thenfour/Clarinoid/CAD/korg microkey-37/switch info.xlsx

switch | contact diode | wire | multiplex channel | selA,B,C | iC Sel | enable | READ
SW1 | D1 | 3 | y3_a | y3 | a | 1 | wire3
SW1 | D2 | 4 | y3_a
SW2 | D3 | 5 | y3_a
SW2 | D4 | 6 | y3_a
SW3 | D5 | 7 | y3_a
SW3 | D6 | 8 | y3_a
SW4 | D7 | 9 | y3_a
SW4 | D8 | 10 | y3_a
SW5 | D9 | 3 | y4_a
SW5 | D10 | 4 | y4_a
SW6 | D11 | 5 | y4_a
SW6 | D12 | 6 | y4_a
SW7 | D13 | 7 | y4_a
SW7 | D14 | 8 | y4_a
SW8 | D15 | 9 | y4_a
SW8 | D16 | 10 | y4_a
SW9 | D17 | 3 | y5_a
SW9 | D18 | 4 | y5_a
SW10 | D19 | 5 | y5_a
SW10 | D20 | 6 | y5_a
SW11 | D21 | 7 | y5_a
SW11 | D22 | 8 | y5_a
SW12 | D23 | 9 | y5_a
SW12 | D24 | 10 | y5_a
SW13 | D25 | 3 | y6_a
SW13 | D26 | 4 | y6_a
SW14 | D27 | 5 | y6_a
SW14 | D28 | 6 | y6_a
SW15 | D29 | 7 | y6_a
SW15 | D30 | 8 | y6_a
SW16 | D31 | 9 | y6_a
SW16 | D32 | 10 | y6_a
SW17 | D33 | 3 | y7_a
SW17 | D34 | 4 | y7_a
SW18 | D35 | 5 | y7_a
SW18 | D36 | 6 | y7_a
SW19 | D37 | 7 | y7_a
SW19 | D38 | 8 | y7_a
SW20 | D39 | 9 | y7_a
SW20 | D40 | 10 | y7_a
SW21 | D41 | 3 | y0_b
SW21 | D42 | 4 | y0_b
SW22 | D43 | 5 | y0_b
SW22 | D44 | 6 | y0_b
SW23 | D45 | 7 | y0_b
SW23 | D46 | 8 | y0_b
SW24 | D47 | 9 | y0_b
SW24 | D48 | 10 | y0_b
SW25 | D49 | 3 | y1_b
SW25 | D50 | 4 | y1_b
SW26 | D51 | 5 | y1_b
SW26 | D52 | 6 | y1_b
SW27 | D53 | 7 | y1_b
SW27 | D54 | 8 | y1_b
SW28 | D55 | 9 | y1_b
SW28 | D56 | 10 | y1_b
SW29 | D57 | 3 | y2_b
SW29 | D58 | 4 | y2_b
SW30 | D59 | 5 | y2_b
SW30 | D60 | 6 | y2_b
SW31 | D61 | 7 | y2_b
SW31 | D62 | 8 | y2_b
SW32 | D63 | 9 | y2_b
SW32 | D64 | 10 | y2_b
SW33 | D65 | 3 | y3_b
SW33 | D66 | 4 | y3_b
SW34 | D67 | 5 | y3_b
SW34 | D68 | 6 | y3_b
SW35 | D69 | 7 | y3_b
SW35 | D70 | 8 | y3_b
SW36 | D71 | 9 | y3_b
SW36 | D72 | 10 | y3_b
SW37 | D73 | 3 | y4_b
SW37 | D74 | 4 | y4_b
