thenfour/Clarinoid/src/clarinoid/basic/Serialization.hpp

// TODO: maximum string size and possibly other sanity checks

#pragma once

#include <type_traits>
#include "BaseDefs.hpp"

#ifdef CLARINOID_PLATFORM_X86
#include <map>
#endif

namespace clarinoid
{

struct IStream
{
    virtual size_t write(const uint8_t *buf, size_t bytes) = 0;
    virtual size_t read(uint8_t *buf, size_t bytes) = 0;
    virtual int readByte() = 0;
    virtual size_t flushWrite() = 0;
};

struct StreamStream : IStream
{
    ::Stream &mStream;
    StreamStream(::Stream &s) : mStream(s)
    {
    }
    virtual size_t write(const uint8_t *buf, size_t bytes) override
    {
        return mStream.write(buf, bytes);
    }

    virtual size_t read(uint8_t *buf, size_t bytes) override
    {
        return mStream.readBytes((char *)buf, bytes);
    }

    virtual int readByte() override
    {
        uint8_t ret;
        return !!read(&ret, 1) ? (int)ret : (int)-1;
    }
    virtual size_t flushWrite() override
    {
        return 0;
    }
};

struct IPeekableStream : IStream
{
    // return <0 if failure
    virtual int peekByte() = 0;
};

struct BufferedStream : IPeekableStream
{
    static constexpr size_t BufferSize = gBufferedStreamBufferSize;
    IStream &mStream;
    uint8_t mBuffer[BufferSize]{0};
    size_t mBufferUsed = 0;
    size_t mReadBufferCursor = 0;

    BufferedStream(IStream &stream) : mStream(stream)
    {
    }

    virtual size_t write(const uint8_t *buf, size_t bytes) override
    {
        size_t ret = 0;
        while (bytes > 0)
        {
            size_t toWriteToBuffer = std::min(bytes, BufferSize - mBufferUsed);
            memcpy(mBuffer + mBufferUsed, buf, toWriteToBuffer);
            mBufferUsed += toWriteToBuffer;
            ret += toWriteToBuffer;
            if (mBufferUsed >= BufferSize)
            {
                size_t written = flushWrite();
                if (written != BufferSize)
                {
                    // something went wrong with underlying stream. likely unusable past this state.
                    int bytesFailed = (int)BufferSize - (int)written;
                    return ret - bytesFailed;
                }
            }
            buf += toWriteToBuffer;
            bytes -= toWriteToBuffer;
        }
        return ret;
    }

    virtual int readByte() override
    {
        uint8_t ret;
        return !!read(&ret, 1) ? (int)ret : (int)-1;
    }

    virtual size_t flushWrite() override
    {
        size_t ret = mStream.write(mBuffer, mBufferUsed);
        mBufferUsed = 0;
        return ret;
    }

    virtual size_t read(uint8_t *buf, size_t bytes) override
    {
        size_t ret = 0;
        while (bytes && EnsureBufferHasUnreadContent())
        {
            size_t unreadBufferBytes = mBufferUsed - mReadBufferCursor;
            size_t bufferBytesToRead = std::min(bytes, unreadBufferBytes);
            memcpy(buf, mBuffer + mReadBufferCursor, bufferBytesToRead);
            mReadBufferCursor += bufferBytesToRead;
            ret += bufferBytesToRead;
            buf += bufferBytesToRead;
            bytes -= bufferBytesToRead;
        }
        return ret;
    }

    virtual int peekByte() override
    {
        if (!EnsureBufferHasUnreadContent())
        {
            return -1;
        }
        return mBuffer[mReadBufferCursor];
    }

    // tries to make sure there's at least 1 unbyte in the buffer.
    // if unable to get even 1 byte, returns false.
    bool EnsureBufferHasUnreadContent()
    {
        // if there's no more buffer to read
        if (mReadBufferCursor >= mBufferUsed)
        {
            // get a fresh buffer.
            mBufferUsed = mStream.read(mBuffer, BufferSize);
            mReadBufferCursor = 0;
            return mBufferUsed > 0;
        }
        return mBufferUsed != 0;
    }
};

enum class TokenType
{
    Syntax,
    Whitespace,
    Keyname,
    StringVal,
    EnumStringVal,
    NumberVal,
    Null,
    BoolValue,
};

struct TextStream : IPeekableStream
{
    IPeekableStream &mStream;
    // 1-based per convention
    uint32_t mLine = 1;
    uint32_t mColumn = 1;
    
    bool mMinified = true;

    TextStream(IPeekableStream &stream) : mStream(stream)
    {
    }

  private:
    virtual size_t write(const uint8_t *buf, size_t bytes) override
    {
        return mStream.write(buf, bytes);
    }

    virtual size_t read(uint8_t *buf, size_t bytes) override
    {
        return mStream.read(buf, bytes);
    }

  public:
#ifdef CLARINOID_PLATFORM_X86

    static const char *TokenTypeToString(TokenType t)
    {
        switch (t)
        {
        case TokenType::Keyname:
            return "keyname";
        case TokenType::EnumStringVal:
            return "enum   ";
        case TokenType::NumberVal:
            return "number ";
        case TokenType::StringVal:
            return "string ";
        case TokenType::Syntax:
            return "syntax ";
        case TokenType::Whitespace:
            return "whites ";
        case TokenType::Null:
            return "null   ";
        case TokenType::BoolValue:
            return "boolval";
        }
        return "?";
    }

    struct SpecificTokenInfo
    {
        std::string mToken;
        int mBytes;
    };

    struct TokenInfo
    {
        std::map<std::string, SpecificTokenInfo> mWrites;
        int mBytes = 0;
    };

    std::map<TokenType, TokenInfo> mStats;

    void DumpStats()
    {
        std::cout << std::endl;
        int total = 0;
        for (auto &kv : mStats)
        {
            std::cout << TokenTypeToString(kv.first) << ": " << kv.second.mBytes << " bytes" << std::endl;

            std::vector<TextStream::SpecificTokenInfo> writes;
            for (auto &tokinfo : kv.second.mWrites)
            {
                writes.push_back(tokinfo.second);
            }

            auto sortFn = [](const TextStream::SpecificTokenInfo &a, const TextStream::SpecificTokenInfo &b) -> bool {
                return a.mBytes > b.mBytes;
            };

            std::sort(writes.begin(), writes.end(), sortFn);

            for (size_t i = 0; i < std::min((size_t)20, writes.size()); ++i)
            {
                std::cout << "    "  << writes[i].mBytes << ": " << writes[i].mToken << std::endl;
            }

            total += kv.second.mBytes;
        }
        std::cout << total << " total bytes " << std::endl;



    }

    std::string mIncompleteStringToken;
    bool mIsCollectingString = false;
    TokenType mCollectingType = TokenType::StringVal; // doesn't matter.

    void BeginToken(TokenType type)
    {
        CCASSERT(!mIsCollectingString);
        mIncompleteStringToken.clear();
        mIsCollectingString = true;
        mCollectingType = type;
    }
    void EndToken()
    {
        CCASSERT(mIsCollectingString);
        mIsCollectingString = false;
        CollectStat(mIncompleteStringToken.c_str(), mCollectingType);
        mIncompleteStringToken.clear();
    }

    void CollectStat(const String &s, TokenType type)
    {
        if (mIsCollectingString)
        {
            mIncompleteStringToken += s.c_str();
        }
        else
        {
            auto &info = mStats[type];
            info.mBytes += (int)s.length();
            auto &sinfo = info.mWrites[s.c_str()];
            sinfo.mBytes += (int)s.length();
            sinfo.mToken = s.c_str();
        }
    }

#else
    void BeginToken(TokenType type)
    {
    }
    void EndToken()
    {
    }

#endif

    size_t write(const String &s, TokenType type)
    {
        if ((type == TokenType::Whitespace) && mMinified)
            return s.length();

#ifdef CLARINOID_PLATFORM_X86
        CollectStat(s, type);
#endif

        size_t ret = mStream.write((const uint8_t *)s.c_str(), s.length());
        for (size_t i = 0; i < ret; ++i)
        {
            interpretChar(s[i]);
        }
        return ret;
    }

    // Reads one byte, or returns -1
    virtual int readByte() override
    {
        int ch = mStream.readByte();
        if (ch <= 0)
            return ch;
        interpretChar(ch);
        return ch;
    }

    virtual int peekByte() override
    {
        return mStream.peekByte();
    }

    virtual size_t flushWrite() override
    {
        return mStream.flushWrite();
    }

  private:
    void interpretChar(char ch)
    {
        if (ch == '\n')
        {
            mLine++;
            mColumn = 1;
            return;
        }
        mColumn++;
    }
};

namespace CCJSON
{

    bool gQuoteKeyNames = false;

template <typename T, typename F_>
T alias_cast(F_ raw_data)
{
    union {
        F_ raw;
        T data;
    } z;
    z.raw = raw_data;
    return z.data;
}

template <bool Condition, class TrueType, class FalseType>
struct conditional
{
    typedef TrueType type;
};

template <class TrueType, class FalseType>
struct conditional<false, TrueType, FalseType>
{
    typedef FalseType type;
};

template <typename A, typename B>
struct choose_largest : conditional<(sizeof(A) > sizeof(B)), A, B>
{
};

typedef double Float;
typedef int64_t Integer;
typedef uint64_t UInt;

enum class NumberType : uint8_t
{
    Undefined,
    Float,
    Integer,
    UInteger,
};

struct EscapeSequence
{
    // returns the json char after escape slash, for the given string character.
    // returns 0 if this char does not need escaping.
    static char escapeChar(char c)
    {
        const char *p = escapeTable(true);
        while (p[0] && p[1] != c)
        {
            p += 2;
        }
        return p[0];
    }
    // accepts a json char after slash, and returns the actual string char.
    // returns 0 if this is not a recognized escape sequence.
    static char unescapeChar(char c)
    {
        const char *p = escapeTable(false);
        for (;;)
        {
            if (p[0] == '\0')
                return 0;
            if (p[0] == c)
                return p[1];
            p += 2;
        }
    }

  private:
    static const char *escapeTable(bool excludeSolidus)
    {
        // groups of 2 chars; 1st char is the incoming char after an escape char ('\')
        // 2nd char is the actual char to output.
        return &"//\"\"\\\\b\bf\fn\nr\rt\t"[excludeSolidus ? 2 : 0];
    }
};

template <typename T, size_t = sizeof(T)>
struct FloatTraits
{
};

template <typename T>
struct FloatTraits<T, sizeof(double)>
{
    typedef uint64_t mantissa_type;
    static const short mantissa_bits = 52;
    static const mantissa_type mantissa_max = (mantissa_type(1) << mantissa_bits) - 1;

    typedef int16_t exponent_type;
    static const exponent_type exponent_max = 308;

    template <typename TExponent>
    static T make_float(T m, TExponent e)
    {
        if (e > 0)
        {
            for (uint8_t index = 0; e != 0; index++)
            {
                if (e & 1)
                    m *= positiveBinaryPowerOfTen(index);
                e >>= 1;
            }
        }
        else
        {
            e = TExponent(-e);
            for (uint8_t index = 0; e != 0; index++)
            {
                if (e & 1)
                    m *= negativeBinaryPowerOfTen(index);
                e >>= 1;
            }
        }
        return m;
    }

    static T positiveBinaryPowerOfTen(int index)
    {
        static uint32_t const factors[] PROGMEM = {
            0x40240000,
            0x00000000, // 1e1
            0x40590000,
            0x00000000, // 1e2
            0x40C38800,
            0x00000000, // 1e4
            0x4197D784,
            0x00000000, // 1e8
            0x4341C379,
            0x37E08000, // 1e16
            0x4693B8B5,
            0xB5056E17, // 1e32
            0x4D384F03,
            0xE93FF9F5, // 1e64
            0x5A827748,
            0xF9301D32, // 1e128
            0x75154FDD,
            0x7F73BF3C // 1e256
        };
        return forge(factors[2 * index], factors[2 * index + 1]);
    }

    static T negativeBinaryPowerOfTen(int index)
    {
        static uint32_t const factors[] PROGMEM = {
            0x3FB99999,
            0x9999999A, // 1e-1
            0x3F847AE1,
            0x47AE147B, // 1e-2
            0x3F1A36E2,
            0xEB1C432D, // 1e-4
            0x3E45798E,
            0xE2308C3A, // 1e-8
            0x3C9CD2B2,
            0x97D889BC, // 1e-16
            0x3949F623,
            0xD5A8A733, // 1e-32
            0x32A50FFD,
            0x44F4A73D, // 1e-64
            0x255BBA08,
            0xCF8C979D, // 1e-128
            0x0AC80628,
            0x64AC6F43 // 1e-256
        };
        return forge(factors[2 * index], factors[2 * index + 1]);
    }

    static T negativeBinaryPowerOfTenPlusOne(int index)
    {
        static uint32_t const factors[] PROGMEM = {
            0x3FF00000,
            0x00000000, // 1e0
            0x3FB99999,
            0x9999999A, // 1e-1
            0x3F50624D,
            0xD2F1A9FC, // 1e-3
            0x3E7AD7F2,
            0x9ABCAF48, // 1e-7
            0x3CD203AF,
            0x9EE75616, // 1e-15
            0x398039D6,
            0x65896880, // 1e-31
            0x32DA53FC,
            0x9631D10D, // 1e-63
            0x25915445,
            0x81B7DEC2, // 1e-127
            0x0AFE07B2,
            0x7DD78B14 // 1e-255
        };
        return forge(factors[2 * index], factors[2 * index + 1]);
    }

    static T nan()
    {
        return forge(0x7ff80000, 0x00000000);
    }

    static T inf()
    {
        return forge(0x7ff00000, 0x00000000);
    }

    static T highest()
    {
        return forge(0x7FEFFFFF, 0xFFFFFFFF);
    }

    static T lowest()
    {
        return forge(0xFFEFFFFF, 0xFFFFFFFF);
    }

    // constructs a double floating point values from its binary representation
    // we use this function to workaround platforms with single precision literals
    // (for example, when -fsingle-precision-constant is passed to GCC)
    static T forge(uint32_t msb, uint32_t lsb)
    {
        return alias_cast<T>((uint64_t(msb) << 32) | lsb);
    }
};

// specialization for 32-bit floats
template <typename T>
struct FloatTraits<T, sizeof(float)>
{
    typedef uint32_t mantissa_type;
    static const short mantissa_bits = 23;
    static const mantissa_type mantissa_max = (mantissa_type(1) << mantissa_bits) - 1;

    typedef int8_t exponent_type;
    static const exponent_type exponent_max = 38;

    template <typename TExponent>
    static T make_float(T m, TExponent e)
    {
        if (e > 0)
        {
            for (uint8_t index = 0; e != 0; index++)
            {
                if (e & 1)
                    m *= positiveBinaryPowerOfTen(index);
                e >>= 1;
            }
        }
        else
        {
            e = -e;
            for (uint8_t index = 0; e != 0; index++)
            {
                if (e & 1)
                    m *= negativeBinaryPowerOfTen(index);
                e >>= 1;
            }
        }
        return m;
    }

    static T positiveBinaryPowerOfTen(int index)
    {
        static uint32_t const factors[] PROGMEM = {
            0x41200000, // 1e1f
            0x42c80000, // 1e2f
            0x461c4000, // 1e4f
            0x4cbebc20, // 1e8f
            0x5a0e1bca, // 1e16f
            0x749dc5ae  // 1e32f
        };
        return forge(factors[index]);
    }

    static T negativeBinaryPowerOfTen(int index)
    {
        static uint32_t const factors[] PROGMEM = {
            0x3dcccccd, // 1e-1f
            0x3c23d70a, // 1e-2f
            0x38d1b717, // 1e-4f
            0x322bcc77, // 1e-8f
            0x24e69595, // 1e-16f
            0x0a4fb11f  // 1e-32f
        };
        return forge(factors[index]);
    }

    static T negativeBinaryPowerOfTenPlusOne(int index)
    {
        static uint32_t const factors[] PROGMEM = {
            0x3f800000, // 1e0f
            0x3dcccccd, // 1e-1f
            0x3a83126f, // 1e-3f
            0x33d6bf95, // 1e-7f
            0x26901d7d, // 1e-15f
            0x0c01ceb3  // 1e-31f
        };
        return forge(factors[index]);
    }

    static T forge(uint32_t bits)
    {
        return alias_cast<T>(bits);
    }

    static T nan()
    {
        return forge(0x7fc00000);
    }

    static T inf()
    {
        return forge(0x7f800000);
    }

    static T highest()
    {
        return forge(0x7f7fffff);
    }

    static T lowest()
    {
        return forge(0xFf7fffff);
    }
};

template <typename TFloat>
struct FloatParts
{
    uint32_t integral;
    uint32_t decimal;
    int16_t exponent;
    int8_t decimalPlaces;

    // Control the exponentiation threshold for big numbers
    // CAUTION: cannot be more that 1e9 !!!!
    static constexpr TFloat POSITIVE_EXPONENTIATION_THRESHOLD = TFloat(1e7);
    static constexpr TFloat NEGATIVE_EXPONENTIATION_THRESHOLD = TFloat(1e-5);

    FloatParts(TFloat value)
    {
        uint32_t maxDecimalPart = sizeof(TFloat) >= 8 ? 1000000000 : 1000000;
        decimalPlaces = sizeof(TFloat) >= 8 ? 9 : 6;

        exponent = normalize(value);

        integral = uint32_t(value);
        // reduce number of decimal places by the number of integral places
        for (uint32_t tmp = integral; tmp >= 10; tmp /= 10)
        {
            maxDecimalPart /= 10;
            decimalPlaces--;
        }

        TFloat remainder = (value - TFloat(integral)) * TFloat(maxDecimalPart);

        decimal = uint32_t(remainder);
        remainder = remainder - TFloat(decimal);

        // rounding:
        // increment by 1 if remainder >= 0.5
        decimal += uint32_t(remainder * 2);
        if (decimal >= maxDecimalPart)
        {
            decimal = 0;
            integral++;
            if (exponent && integral >= 10)
            {
                exponent++;
                integral = 1;
            }
        }

        // remove trailing zeros
        while (decimal % 10 == 0 && decimalPlaces > 0)
        {
            decimal /= 10;
            decimalPlaces--;
        }
    }

    static int16_t normalize(TFloat &value)
    {
        typedef FloatTraits<TFloat> traits;
        int16_t powersOf10 = 0;

        int8_t index = sizeof(TFloat) == 8 ? 8 : 5;
        int bit = 1 << index;

        if (value >= POSITIVE_EXPONENTIATION_THRESHOLD)
        {
            for (; index >= 0; index--)
            {
                if (value >= traits::positiveBinaryPowerOfTen(index))
                {
                    value *= traits::negativeBinaryPowerOfTen(index);
                    powersOf10 = int16_t(powersOf10 + bit);
                }
                bit >>= 1;
            }
        }

        if (value > 0 && value <= NEGATIVE_EXPONENTIATION_THRESHOLD)
        {
            for (; index >= 0; index--)
            {
                if (value < traits::negativeBinaryPowerOfTenPlusOne(index))
                {
                    value *= traits::positiveBinaryPowerOfTen(index);
                    powersOf10 = int16_t(powersOf10 - bit);
                }
                bit >>= 1;
            }
        }

        return powersOf10;
    }
};

String UnsignedIntegerToStringWithOptionalPrefix(UInt value, char prefixChar = 0)
{
    char buffer[24] = {0};
    char *end = buffer + sizeof(buffer) - 1;
    char *begin = end;

    // write the string in reverse order
    do
    {
        *--begin = char(value % 10 + '0');
        value = UInt(value / 10);
    } while (value);

    if (prefixChar)
    {
        *--begin = prefixChar;
    }

    return {begin};
}

String UnsignedIntegerToString(UInt value)
{
    return UnsignedIntegerToStringWithOptionalPrefix(value, 0);
}

String SignedIntegerToString(Integer value)
{
    String ret;
    if (value < 0)
    {
        UInt unsigned_value = UInt(UInt(~value) + 1);
        return ret + UnsignedIntegerToStringWithOptionalPrefix(unsigned_value, '-');
    }
    return UnsignedIntegerToStringWithOptionalPrefix(UInt(value), 0);
}

struct NumberData
{
    NumberType mType = NumberType::Undefined;
    Float mFloatValue = 0;
    Integer mIntValue = 0;
    UInt mUIntValue = 0;

    template <typename T, std::enable_if_t<std::is_floating_point<T>::value, int> = 0>
    void Set(T param)
    {
        mFloatValue = param;
        mType = NumberType::Float;
    }

    template <typename T, std::enable_if_t<std::is_integral<T>::value && std::is_signed<T>::value, int> = 0>
    void Set(T param)
    {
        mIntValue = param;
        mType = NumberType::Integer;
    }

    template <typename T, std::enable_if_t<std::is_integral<T>::value && std::is_unsigned<T>::value, int> = 0>
    void Set(T param)
    {
        mUIntValue = param;
        mType = NumberType::UInteger;
    }

    template <typename T, std::enable_if_t<std::is_floating_point<T>::value || std::is_integral<T>::value, int> = 0>
    T Get() const
    {
        switch (mType)
        {
        case NumberType::Undefined:
        default:
            return 0;
        case NumberType::Float:
            return T(mFloatValue);
        case NumberType::Integer:
            return T(mIntValue);
        case NumberType::UInteger:
            return T(mUIntValue);
        }
    }

    String ToString() const
    {
        switch (mType)
        {
        default:
            return "<invalid;fatal error>";
        case NumberType::Undefined:
            return "<undefined>";
        case NumberType::Float:
            return String("<float>:") + String(mFloatValue);
        case NumberType::Integer:
            return String("<signed>:") + SignedIntegerToString(mIntValue);
        case NumberType::UInteger:
            return String("<unsigned>:") + UnsignedIntegerToString(mUIntValue);
        }
    }
};

// this could be adapted to read from stream, char by char, but it's just simpler to go like this.
inline bool parseNumber(const char *s, NumberData &result)
{
    typedef FloatTraits<Float> traits;
    typedef choose_largest<traits::mantissa_type, UInt>::type mantissa_t;
    typedef traits::exponent_type exponent_t;

    CCASSERT(s != 0);

    bool is_negative = false;
    switch (*s)
    {
    case '-':
        is_negative = true;
        s++;
        break;
    case '+':
        s++;
        break;
    }

    if (!isdigit(*s) && *s != '.')
        return false;

    mantissa_t mantissa = 0;
    exponent_t exponent_offset = 0;
    const mantissa_t maxUint = UInt(-1);

    while (isdigit(*s))
    {
        uint8_t digit = uint8_t(*s - '0');
        if (mantissa > maxUint / 10)
            break;
        mantissa *= 10;
        if (mantissa > maxUint - digit)
            break;
        mantissa += digit;
        s++;
    }

    if (*s == '\0')
    {
        if (is_negative)
        {
            const mantissa_t sintMantissaMax = mantissa_t(1) << (sizeof(Integer) * 8 - 1);
            if (mantissa <= sintMantissaMax)
            {
                result.Set(Integer(~mantissa + 1));
                return true;
            }
        }
        else
        {
            result.Set(UInt(mantissa));
            return true;
        }
    }

    // avoid mantissa overflow
    while (mantissa > traits::mantissa_max)
    {
        mantissa /= 10;
        exponent_offset++;
    }

    // remaing digits can't fit in the mantissa
    while (isdigit(*s))
    {
        exponent_offset++;
        s++;
    }

    if (*s == '.')
    {
        s++;
        while (isdigit(*s))
        {
            if (mantissa < traits::mantissa_max / 10)
            {
                mantissa = mantissa * 10 + uint8_t(*s - '0');
                exponent_offset--;
            }
            s++;
        }
    }

    int exponent = 0;
    if (*s == 'e' || *s == 'E')
    {
        s++;
        bool negative_exponent = false;
        if (*s == '-')
        {
            negative_exponent = true;
            s++;
        }
        else if (*s == '+')
        {
            s++;
        }

        while (isdigit(*s))
        {
            exponent = exponent * 10 + (*s - '0');
            if (exponent + exponent_offset > traits::exponent_max)
            {
                if (negative_exponent)
                    result.Set(is_negative ? -0.0f : 0.0f);
                else
                    result.Set(is_negative ? -traits::inf() : traits::inf());
                return true;
            }
            s++;
        }
        if (negative_exponent)
            exponent = -exponent;
    }
    exponent += exponent_offset;

    // we should be at the end of the string, otherwise it's an error
    if (*s != '\0')
        return false;

    Float final_result = traits::make_float(static_cast<Float>(mantissa), exponent);

    result.Set(is_negative ? -final_result : final_result);

    return true;
}

static char gUnquotedTokenChars[] = "0123456789_abcdefghijklmnopqrstuvwxyzABCDEFGHIJKLMNOPQRSTUVWXYZ";
static char gUnquotedTokenStartChars[] = "_abcdefghijklmnopqrstuvwxyzABCDEFGHIJKLMNOPQRSTUVWXYZ";


} // namespace CCJSON

enum class JsonDataType : uint8_t
{
    EndOfList,
    Undefined,
    Null,
    Number,
    String,
    Boolean,
    Array,
    Object,
};

////////////////////////////////////////////////////////////////////////////////////////////////////////////
// requirements of implementer:
// - non-copyable (delete copy ctor & operator =())
// - when creating child objects, call ExpectChildStreamAccess(), then construct with parent. default ctor should use
// nullptr
// - when accessing the stream, call OnStreamAccess() to perform checks & notify parent who's the currently active child
// - destructor call OnDestructor();
struct JsonParentChildHelper
{
  protected:
    bool mIsLocked = false;

  private:
    JsonParentChildHelper *mParent = nullptr;
    JsonParentChildHelper *mCurrentChild = nullptr;
    bool mExpectingChild = false;

    // called from a child when it's being destructed.
    void OnChildDestroy(JsonParentChildHelper *child)
    {
        // if a child is destructing but not the one we're tracking, then we don't really care; it's some intermediate
        // object
        if (mCurrentChild == child)
        {
            child->EnsureClosed();
            mCurrentChild = nullptr;
        }
    }

    void OnChildCreate(JsonParentChildHelper *child)
    {
        if (mCurrentChild)
        {
            mCurrentChild->EnsureClosed();
        }
        mCurrentChild = child;
    }

  protected:
    // no duplicates allowed because parents keep track of children.
    JsonParentChildHelper(const JsonParentChildHelper &s) = delete;
    JsonParentChildHelper &operator=(const JsonParentChildHelper &s) = delete;

    // but moves are OK;
    explicit JsonParentChildHelper(JsonParentChildHelper &&rhs) = default;

    // parent may be nullptr
    explicit JsonParentChildHelper(JsonParentChildHelper *parent) : mParent(parent) //, mNodeID(CCJSON::GetNextID())
    {
    }

    virtual ~JsonParentChildHelper()
    {
        if (this->mCurrentChild)
        {
            // this would leave a child with an invalid parent pointer
            CCASSERT(false);
        }
    }

    virtual void EnsureClosed() = 0;

    void OnDestructor()
    {
        if (mParent)
        {
            mParent->OnChildDestroy(this);
        }
    }

    // return true if we already know we're closed (because we're locked).
    bool EnsureChildrenClosed()
    {
        if (mIsLocked)
            return true;
        if (mCurrentChild)
        {
            mCurrentChild->EnsureClosed();
        }
        return false;
    }

    void OnStreamAccess()
    {
        if (mParent)
        {
            mParent->SetCurrentlyAccessingChild(this);
        }
    }

    void SetCurrentlyAccessingChild(JsonParentChildHelper *child)
    {
        CCASSERT(child != this);
        // there are a number of assertions we could do here to ensure order of certain operations, but it's precarious
        // and complex so count on other symptoms of errors.

        if (child != mCurrentChild && mCurrentChild)
        {
            CCASSERT(mCurrentChild->mIsLocked); // changing children; make sure that the previous children finished.
        }

        mCurrentChild = child;
        mExpectingChild = false;
    }

    // call when you are done with current child and will move to a next (maybe)
    void ExpectChildStreamAccess()
    {
        // if this is true, it means you were already expecting child activity, before expecting another one.
        // it means you created multiple child values without using them. probably coding something out of order.
        CCASSERT(!mExpectingChild);
        if (mCurrentChild)
        {
            mCurrentChild->mIsLocked = true;
        }
        mCurrentChild = nullptr;
        mExpectingChild = true;
    }
};
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
